lanmilab/SSRM_Shield/Design/Outputs/LanmiLab_SSRM_Shield_asm_side_noard.jpg

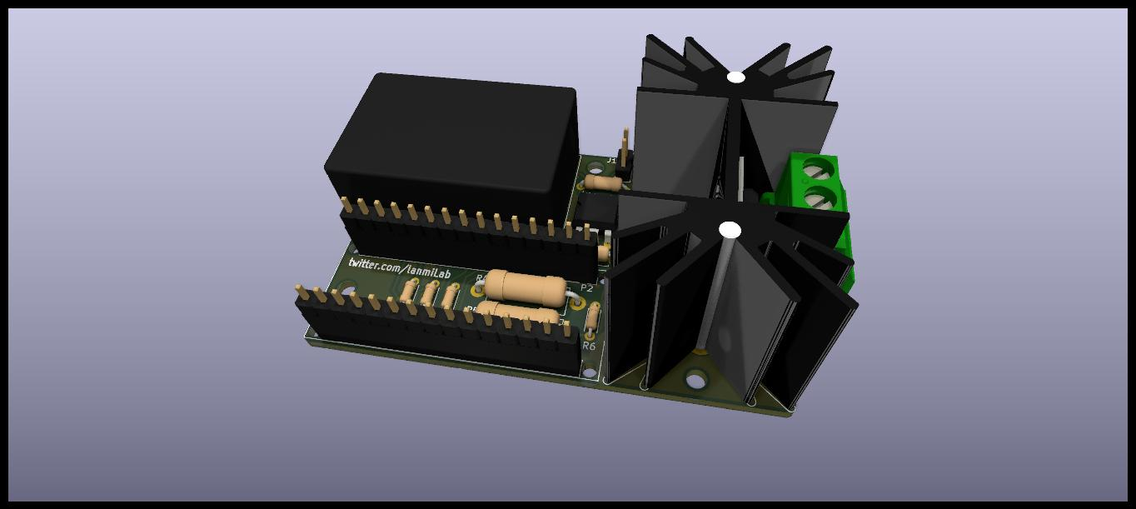
Design/Outputs/LanmiLab_SSRM_Shield_asm_side_noard.jpg
