lanmilab/SSRM_Shield/Design/Outputs/LanmiLab_SSRM_Shield_asm_top.jpg

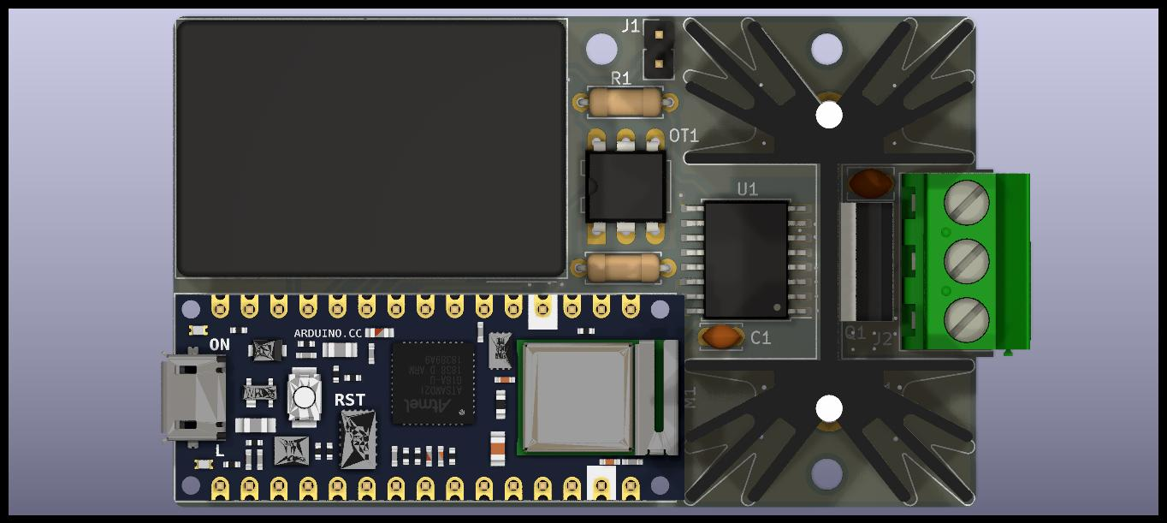
Design/Outputs/LanmiLab_SSRM_Shield_asm_top.jpg
